mario73z/Rotary-Case-Tumbler/INNE/2.jpg

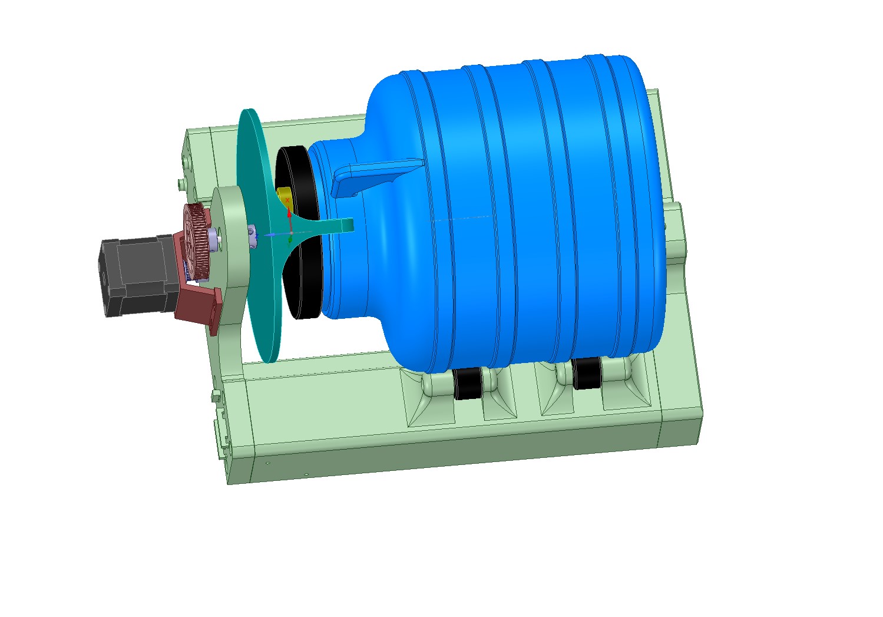
INNE/2.jpg
